hgimonet/IDD_spring2021_Final_SayCheese/CollaBoard/emojis/balloon_1f388.png

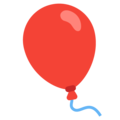
CollaBoard/emojis/balloon_1f388.png
