hgimonet/IDD_spring2021_Final_SayCheese/CollaBoard/emojis/bottle-with-popping-cork_1f37e.png

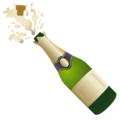
CollaBoard/emojis/bottle-with-popping-cork_1f37e.png
