hgimonet/IDD_spring2021_Final_SayCheese/CollaBoard/emojis/globe-showing-americas_1f30e.png

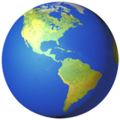
CollaBoard/emojis/globe-showing-americas_1f30e.png
