hgimonet/IDD_spring2021_Final_SayCheese/CollaBoard/emojis/graduation-cap_1f393.png

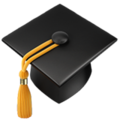
CollaBoard/emojis/graduation-cap_1f393.png
