hgimonet/IDD_spring2021_Final_SayCheese/CollaBoard/emojis/light-bulb_1f4a1.png

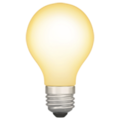
CollaBoard/emojis/light-bulb_1f4a1.png
