hgimonet/IDD_spring2021_Final_SayCheese/CollaBoard/emojis/waving-hand_1f44b.png

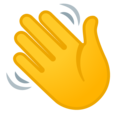
CollaBoard/emojis/waving-hand_1f44b.png
